JFost146/EWOD-RF-Switch-FYP/Liquid Switch Test Results/Liquid VNA Tests/CSV/line_vias_on_excel.csv

!CSV A.01.01
!Agilent Technologies | E8362C | MY43020457 | A.09.42.15
!Agilent E8362C: A.09.42.15
!Date: Wednesday | November 26 | 2025 12:28:25
!Source: Standard
BEGIN CH1_DATA
Freq(Hz) | S11(DB) | S11(DEG) | S12(DB) | S12(DEG) | S21(DB) | S21(DEG) | S22(DB) | S22(DEG)
10000000 | -56.577438 | -7.4895058 | -0.022123341 | -1.2580889 | -0.010961204 | -1.2239869 | -50.919029 | 54.015999
16243750 | -55.531376 | 23.370153 | -0.010499125 | -2.0344646 | -0.0018594628 | -2.0382662 | -54.275063 | 7.492342
22487500 | -55.183769 | 24.9179 | -0.012341504 | -2.822902 | -0.0068679964 | -2.800246 | -52.201286 | -11.672682
28731250 | -54.840683 | 0.24963163 | -0.01239315 | -3.598273 | -0.0085058007 | -3.5693867 | -52.06871 | -24.312008
34975000 | -52.589417 | -9.9814119 | -0.014698834 | -4.3900676 | -0.011280322 | -4.350389 | -54.125645 | -21.24522
41218750 | -51.092468 | -17.048319 | -0.015594626 | -5.1610789 | -0.011030254 | -5.1357045 | -54.29306 | -34.084538
47462500 | -51.67923 | -26.576786 | -0.013667384 | -5.9032698 | -0.017841551 | -5.9189105 | -53.513065 | -60.86919
53706250 | -52.835781 | 53.624355 | -0.018885307 | -6.6789079 | -0.026464261 | -6.650991 | -57.206219 | 79.034088
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
