JFost146/EWOD-RF-Switch-FYP/Liquid Switch Test Results/Liquid VNA Tests/CSV/off_empty_s2.csv

!CSV A.01.01
!Agilent Technologies | E8362C | MY43020457 | A.09.42.15
!Agilent E8362C: A.09.42.15
!Date: Friday | March 13 | 2026 13:57:07
!Source: Standard
BEGIN CH1_DATA
Freq(Hz) | S11(DB) | S11(DEG) | S12(DB) | S12(DEG) | S21(DB) | S21(DEG) | S22(DB) | S22(DEG)
10000000 | -42.446312 | -65.891113 | -0.12213615 | -0.45993614 | -0.070999883 | -0.63881087 | -90.51886 | -8.0306559
10309375 | -42.312195 | -12.37982 | -0.074650802 | -0.95617956 | -0.017632166 | -0.2635771 | -97.118378 | 101.10272
10618750 | -35.713432 | -26.69989 | -0.19302882 | -0.98117131 | -0.075846612 | -0.85168248 | -99.432892 | 136.01479
10928125 | -44.31744 | -102.2533 | 0.010342653 | -1.0486437 | 0.029242586 | -0.76505142 | -96.585014 | -72.983299
11237500 | -43.104214 | -147.15491 | -0.013406839 | -1.3844543 | -0.0031921384 | -0.6232968 | -103.08385 | -149.97713
11546875 | -38.392101 | -67.251915 | -0.070585854 | -0.90426016 | -0.037777554 | -0.9227494 | -106.08732 | -87.16069
11856250 | -49.788097 | 68.314018 | -0.10141768 | -1.2113678 | -0.0099001583 | -0.82335001 | -102.72053 | 122.2586
12165625 | -39.291985 | -99.804344 | -0.068781249 | -0.842237 | 0.058634348 | -0.78473234 | -114.4126 | -138.27721
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
