JFost146/EWOD-RF-Switch-FYP/Liquid Switch Test Results/Liquid VNA Tests/CSV/off_empty_s2_10G.csv

!CSV A.01.01
!Agilent Technologies | E8362C | MY43020457 | A.09.42.15
!Agilent E8362C: A.09.42.15
!Date: Friday | March 13 | 2026 14:46:22
!Source: Standard
BEGIN CH1_DATA
Freq(Hz) | S11(DB) | S11(DEG) | S12(DB) | S12(DEG) | S21(DB) | S21(DEG) | S22(DB) | S22(DEG)
10000000 | -40.973312 | -90.109108 | -0.023841988 | -0.72925091 | -0.01262271 | -0.65966314 | -45.487076 | -133.0667
10499500 | -43.463398 | -134.61723 | -0.023797434 | -0.88658255 | -9.1616377e-005 | -0.45673135 | -41.247387 | 73.512367
10999000 | -44.390884 | -54.08474 | 0.034872752 | -0.88684946 | -0.042908262 | -0.91289151 | -44.989479 | -107.27928
11498500 | -42.310959 | -139.7755 | -0.027657457 | -0.94823295 | -0.013115765 | -0.42339656 | -53.518703 | -133.86609
11998000 | -42.868809 | 108.02074 | -0.017330037 | -0.88571042 | -0.061615203 | -0.74741912 | -45.352215 | -142.23566
12497500 | -55.956398 | -35.587605 | 0.0013233895 | -0.83230472 | 0.029814795 | -0.97863913 | -45.361553 | -144.95697
12997000 | -50.189701 | 20.434099 | -0.035646047 | -1.0399227 | -0.046510186 | -0.93699259 | -42.755562 | -100.8826
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
