JFost146/EWOD-RF-Switch-FYP/Liquid Switch Test Results/Liquid VNA Tests/CSV/on_empty_LM.csv

!CSV A.01.01
!Agilent Technologies | E8362C | MY43020457 | A.09.42.15
!Agilent E8362C: A.09.42.15
!Date: Friday | March 13 | 2026 14:12:07
!Source: Standard
BEGIN CH1_DATA
Freq(Hz) | S11(DB) | S11(DEG) | S12(DB) | S12(DEG) | S21(DB) | S21(DEG) | S22(DB) | S22(DEG)
10000000 | 0.024940383 | 179.59671 | -52.544277 | -161.73323 | -50.41732 | 128.3866 | -55.309956 | 56.365803
10309375 | 0.079868101 | 179.45694 | -50.632008 | -119.94695 | -44.596619 | -133.59875 | -60.734818 | -173.62325
10618750 | 0.090754658 | 179.67905 | -51.329712 | -74.394295 | -48.086929 | 54.819515 | -67.624481 | 111.72427
10928125 | 0.051701143 | 179.39047 | -51.713657 | -41.000336 | -47.88567 | 95.725342 | -57.946255 | -138.91432
11237500 | 0.04458699 | 179.41487 | -49.848824 | 121.89231 | -51.005745 | -179.48724 | -65.381668 | 100.32699
11546875 | 0.0027404584 | 179.47963 | -54.048187 | -16.942593 | -50.142876 | 111.74732 | -65.867622 | 152.76817
11856250 | 0.11814078 | 179.27765 | -62.226986 | -18.621017 | -45.788422 | 15.202814 | -63.480057 | 70.262001
12165625 | 0.0063070841 | 179.48099 | -48.925537 | 140.95226 | -45.220955 | 58.431267 | -62.120075 | 109.14835
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
