JFost146/EWOD-RF-Switch-FYP/Liquid Switch Test Results/Liquid VNA Tests/CSV/on_empty_LM_10G.csv

!CSV A.01.01
!Agilent Technologies | E8362C | MY43020457 | A.09.42.15
!Agilent E8362C: A.09.42.15
!Date: Friday | March 13 | 2026 14:56:53
!Source: Standard
BEGIN CH1_DATA
Freq(Hz) | S11(DB) | S11(DEG) | S12(DB) | S12(DEG) | S21(DB) | S21(DEG) | S22(DB) | S22(DEG)
10000000 | -0.02883427 | 179.22401 | -36.853901 | -45.656296 | -53.508907 | 110.72332 | -0.025304871 | 178.8757
10499500 | 0.088024758 | 179.62524 | -42.610073 | 43.6759 | -42.351009 | 88.664299 | 0.073675506 | 179.33986
10999000 | 0.0059062229 | 179.47528 | -46.258221 | -24.885923 | -39.968891 | 161.83246 | 0.0038620646 | 178.79898
11498500 | -0.063495502 | 179.33536 | -45.258469 | 45.443848 | -43.804924 | 143.74675 | -0.039524749 | 179.19449
11998000 | 0.054964911 | 178.73453 | -50.642658 | 31.413338 | -47.187065 | -31.745867 | -0.014563385 | 179.27667
12497500 | 0.099621348 | 178.97057 | -59.108891 | 62.66444 | -46.016521 | 66.363876 | 0.043029137 | 178.81645
12997000 | 0.037598494 | 178.61079 | -50.314598 | 163.02298 | -47.255718 | 3.0066524 | -0.058909055 | 178.63824
13496500 | 0.022129597 | 178.72371 | -54.402306 | 145.51115 | -50.652317 | -95.048813 | 0.0093286689 | 178.79399
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
