JFost146/EWOD-RF-Switch-FYP/Liquid Switch Test Results/Liquid VNA Tests/CSV/on_empty_NaOH_s2.csv

!CSV A.01.01
!Agilent Technologies | E8362C | MY43020457 | A.09.42.15
!Agilent E8362C: A.09.42.15
!Date: Friday | March 13 | 2026 14:08:12
!Source: Standard
BEGIN CH1_DATA
Freq(Hz) | S11(DB) | S11(DEG) | S12(DB) | S12(DEG) | S21(DB) | S21(DEG) | S22(DB) | S22(DEG)
10000000 | -2.896971 | -178.77803 | -18.263798 | 17.991884 | -12.177079 | 3.1861832 | -56.691605 | 56.491653
10309375 | -2.7537498 | -179.69048 | -17.94371 | 19.845844 | -11.972996 | 4.3649793 | -62.254936 | -173.72598
10618750 | -2.7678015 | -178.51598 | -17.974106 | 17.03022 | -11.810124 | 2.9077439 | -69.066872 | 111.4514
10928125 | -2.6832194 | -179.99255 | -17.405386 | 18.373415 | -11.709657 | 4.2081981 | -59.418129 | -139.15356
11237500 | -2.820498 | -179.24667 | -17.30508 | 17.877876 | -11.73575 | 6.1936436 | -66.835976 | 100.04073
11546875 | -2.887605 | -179.62373 | -16.777803 | 17.815899 | -11.634907 | 4.267024 | -67.355362 | 152.52417
11856250 | -2.7066596 | -179.73294 | -16.51836 | 18.238787 | -11.41779 | 5.240624 | -64.931725 | 70.242737
12165625 | -2.7248893 | -179.71129 | -16.646791 | 17.901587 | -11.4345 | 4.4327993 | -63.606407 | 108.85793
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
