JFost146/EWOD-RF-Switch-FYP/Liquid Switch Test Results/Simulations/Figures/compare2.png

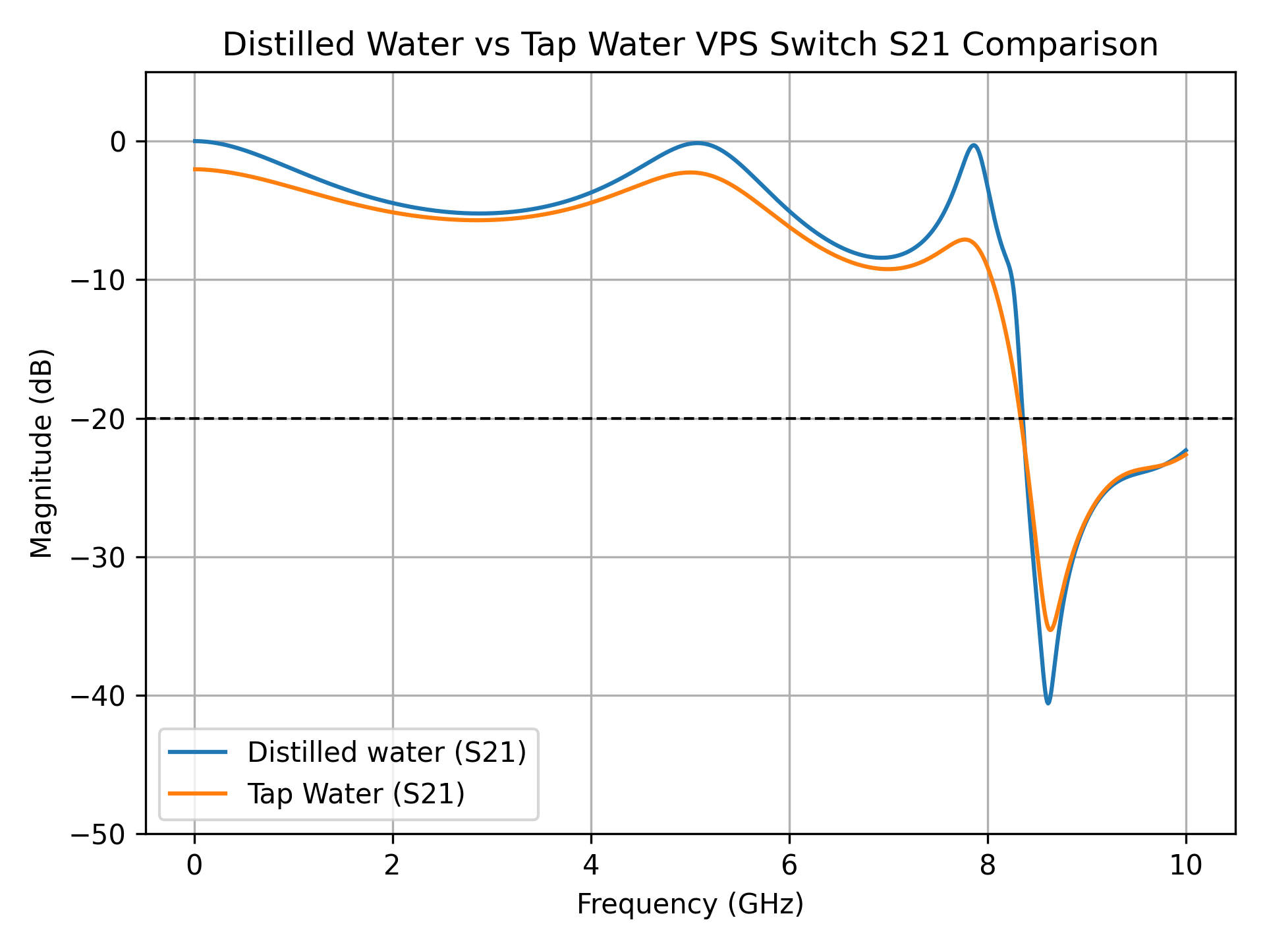
Liquid Switch Test Results/Simulations/Figures/compare2.png
