JFost146/EWOD-RF-Switch-FYP/Liquid Switch Test Results/Simulations/Figures/switch_EGaIn_S11_S21_plot.png

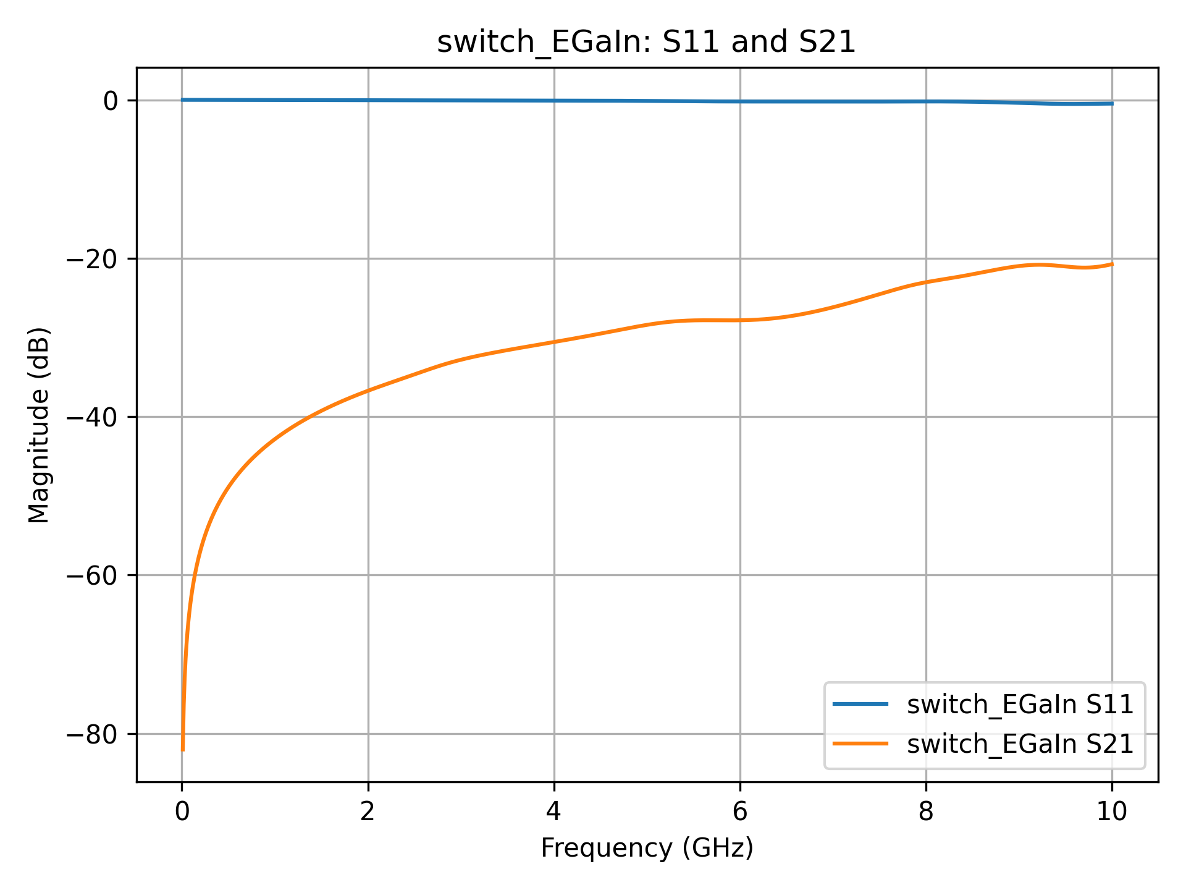
Liquid Switch Test Results/Simulations/Figures/switch_EGaIn_S11_S21_plot.png
